honzab/996_vdo_gauge_driver/996_oil_temp_gauge/version2/version2.kicad_sch

## KiCad design 996_oil_temp_gauge/version2/version2.kicad_sch (2025-05-04)

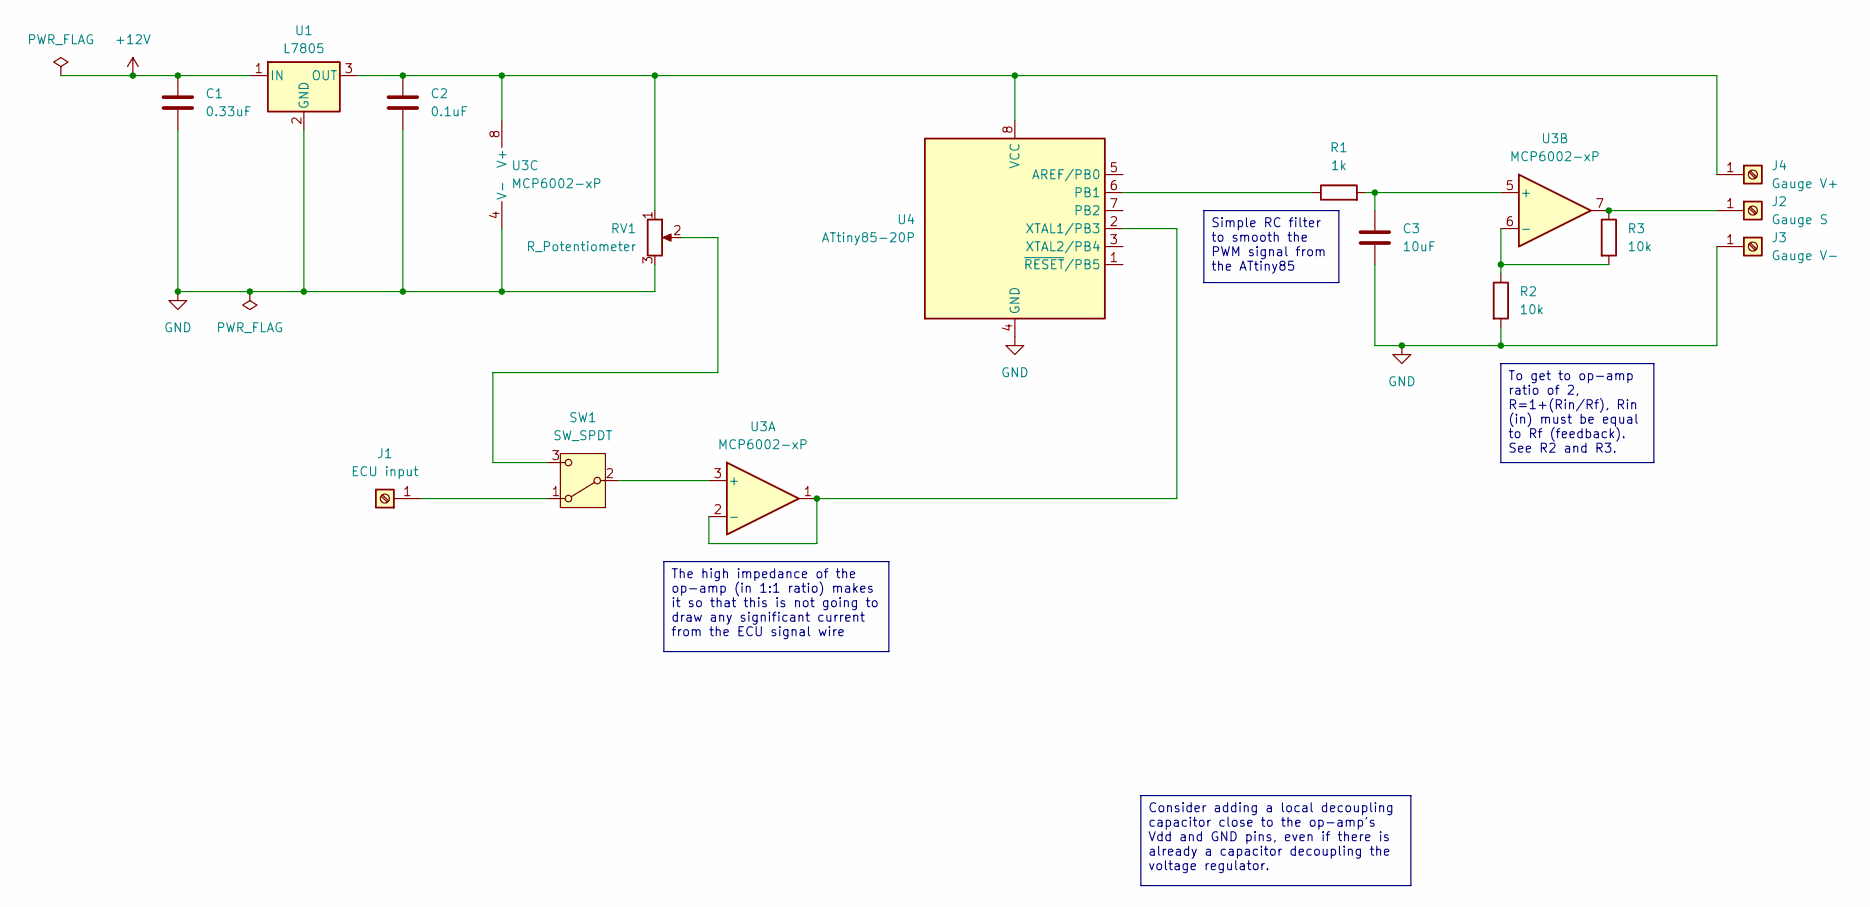
[picture p14: schematic version2.kicad_sch]

Parts:
C1: 0.33uF
C2: 0.1uF
C3: 10uF
J1: ECU input
J2: Gauge S
J3: Gauge V-
J4: Gauge V+
R1: 1k
R2, R3: 10k
RV1: R_Potentiometer
SW1: SW_SPDT
U1: L7805
U3: MCP6002-xP; DIP-8_W7.62mm
U4: ATtiny85-20P; DIP-8_W7.62mm

Connections:
+12V: C1.1, U1.1 (IN)
GND: C1.2, C2.2, C3.2, J3.1, R2.2, RV1.3, U1.2 (GND), U3.4 (V-), U4.4 (GND)
unnamed: C2.1, J4.1, RV1.1, U1.3 (OUT), U3.8 (V+), U4.8 (VCC)
unnamed: C3.1, R1.2, U3.5 (+)
unnamed: J1.1, SW1.1 (A)
unnamed: J2.1, R3.1, U3.7
unnamed: R1.1, U4.6 (PB1)
unnamed: R2.1, R3.2, U3.6 (-)
unnamed: RV1.2, SW1.3 (C)
unnamed: SW1.2 (B), U3.3 (+)
unnamed: U3.1, U3.2 (-), U4.2 (XTAL1/PB3)

Notes on the sheet:
Simple RC filter to smooth the PWM signal from the ATtiny85
Consider adding a local decoupling capacitor close to the op-amp's Vdd and GND pins, even if there is already a capacitor decoupling the voltage regulator.
To get to op-amp ratio of 2, R=1+(Rin/Rf), Rin (in) must be equal to Rf (feedback). See R2 and R3.
The high impedance of the op-amp (in 1:1 ratio) makes it so that this is not going to draw any significant current from the ECU signal wire
